huheran/MoveToPlay/hardware/pcb/Blade_V1.0_Nromal/Blade_V1.0_Nromal_.png

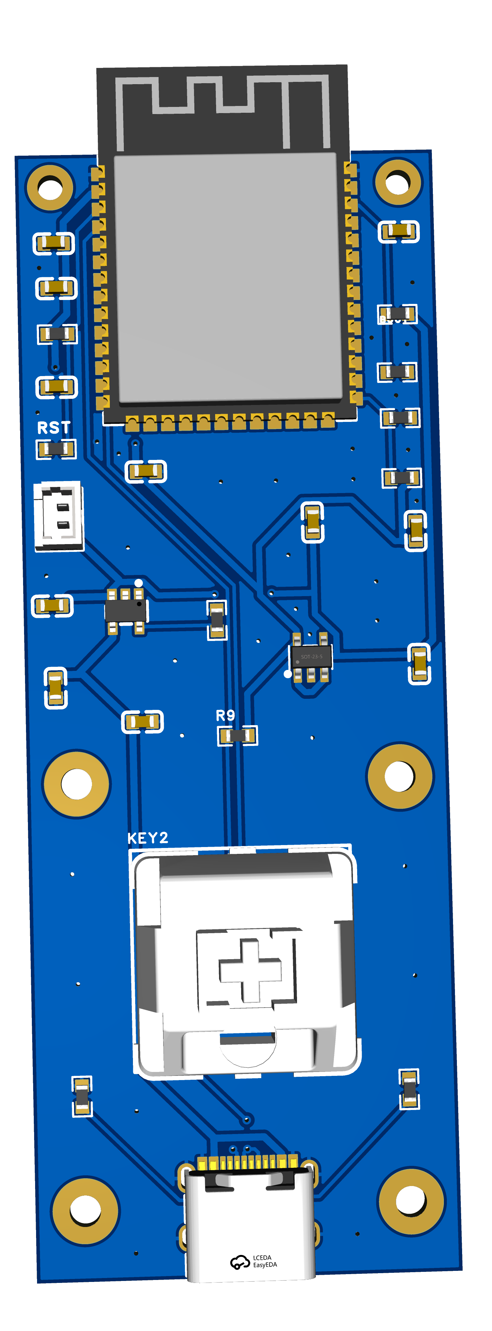
hardware/pcb/Blade_V1.0_Nromal/Blade_V1.0_Nromal_.png
