huheran/MoveToPlay/hardware/pcb/Blade_V2.0_HR(Heart Rate)/Blade_V2.0_HR(Heart Rate)-.png

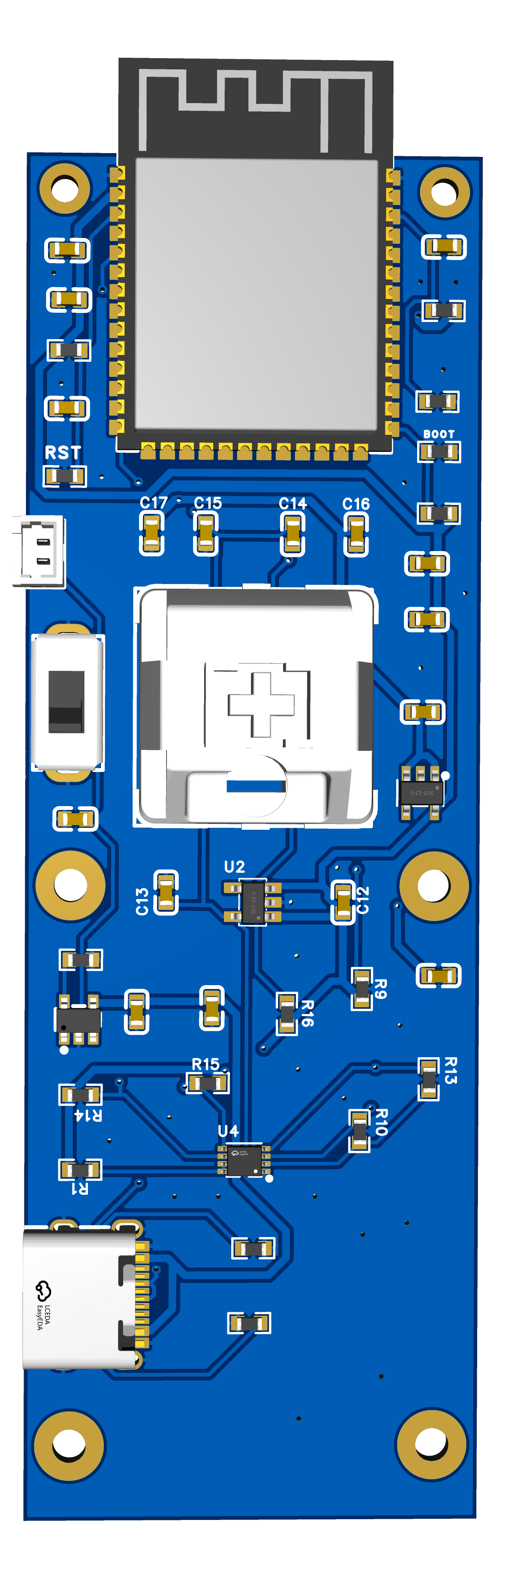
hardware/pcb/Blade_V2.0_HR(Heart Rate)/Blade_V2.0_HR(Heart Rate)-.png
