huheran/MoveToPlay/hardware/pcb/Dongle_SW1/Dongle_SW1.png

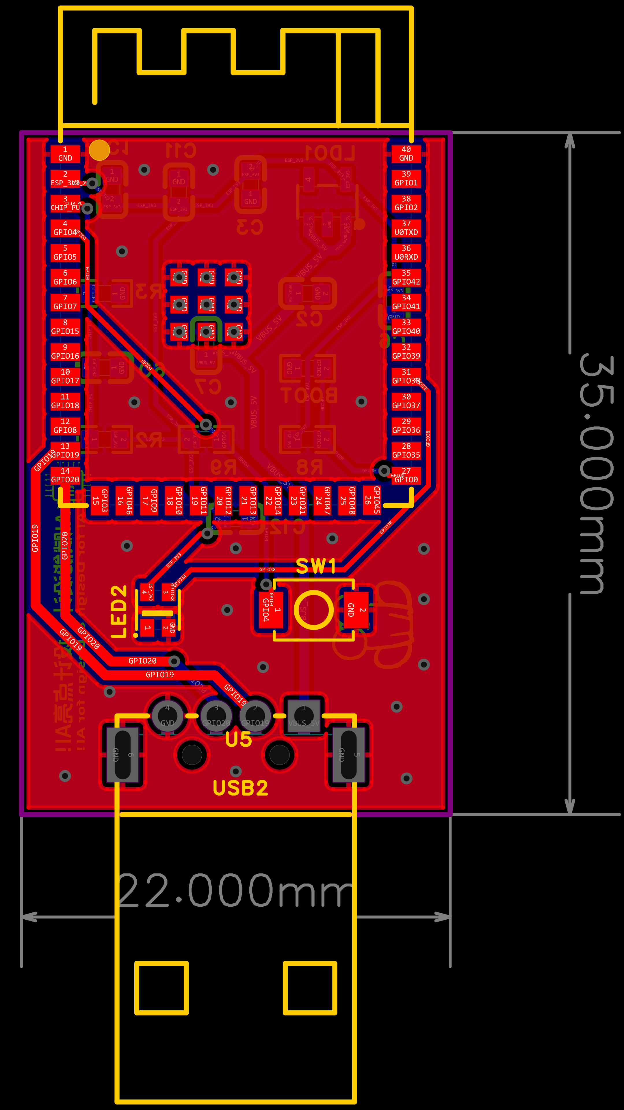
hardware/pcb/Dongle_SW1/Dongle_SW1.png
