huheran/MoveToPlay/hardware/pcb/Dongle_SW3/Dongle_SW3.png

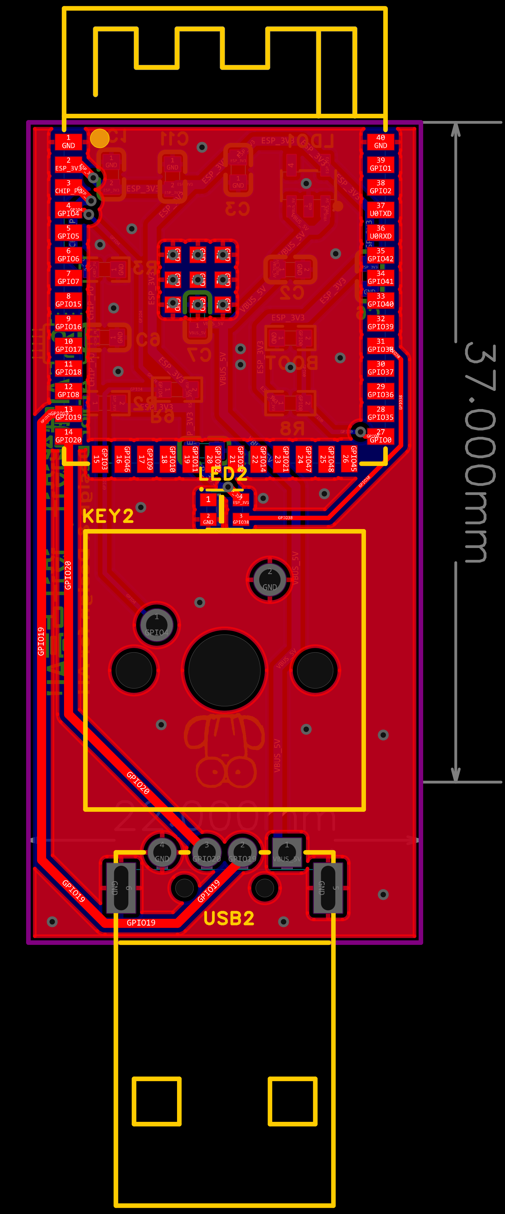
hardware/pcb/Dongle_SW3/Dongle_SW3.png
