huheran/MoveToPlay/hardware/pcb/Heart_Rate_V2.0/Heart_Rate_V2.0.png

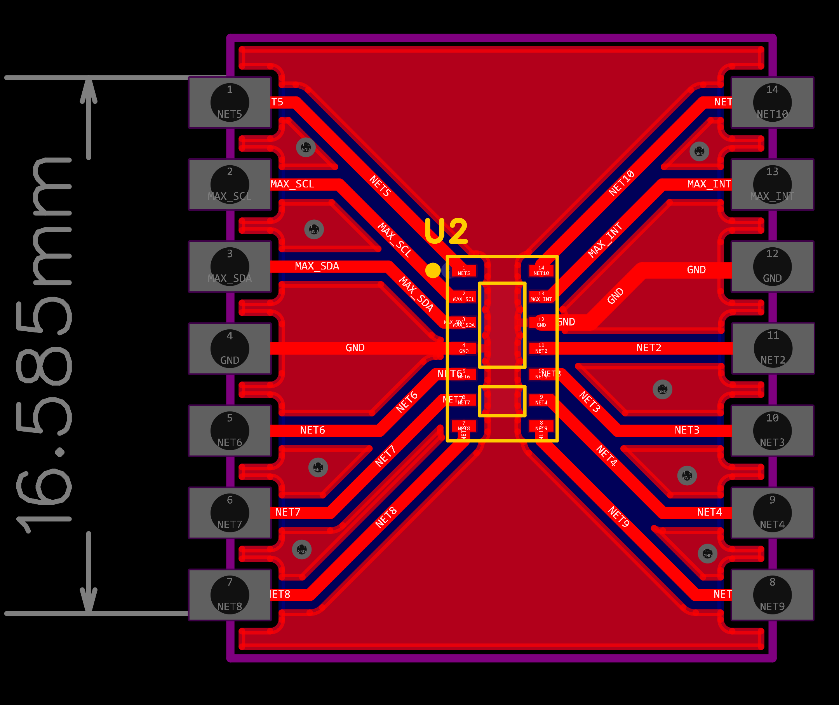
hardware/pcb/Heart_Rate_V2.0/Heart_Rate_V2.0.png
