huheran/MoveToPlay/hardware/pcb/Heart_Rate_V2.0/Heart_Rate_V2.0_.png

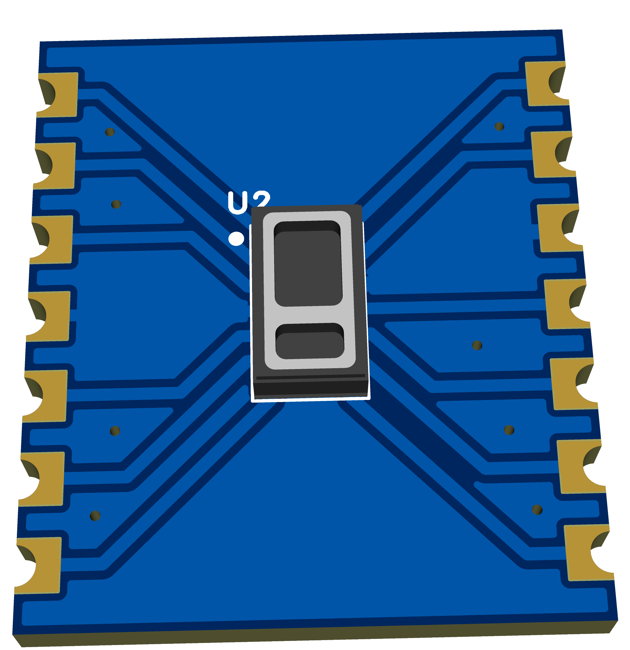
hardware/pcb/Heart_Rate_V2.0/Heart_Rate_V2.0_.png
