huheran/MoveToPlay/hardware/pcb/Tracker_V1.0_Top-Battery/Tracker_V1.0_Top-Battery_.png

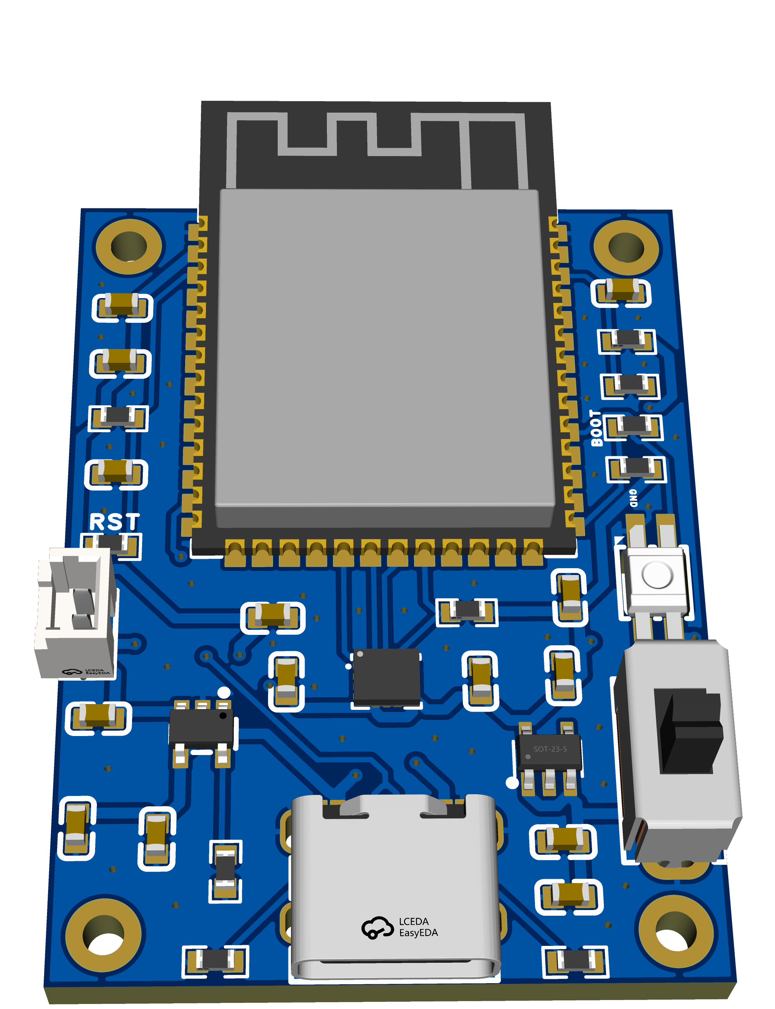
hardware/pcb/Tracker_V1.0_Top-Battery/Tracker_V1.0_Top-Battery_.png
