huheran/MoveToPlay/hardware/pcb/Tracker_V1.0_Top-Battery_SMT/Tracker_V1.0_SMT_Top-Battery-.png

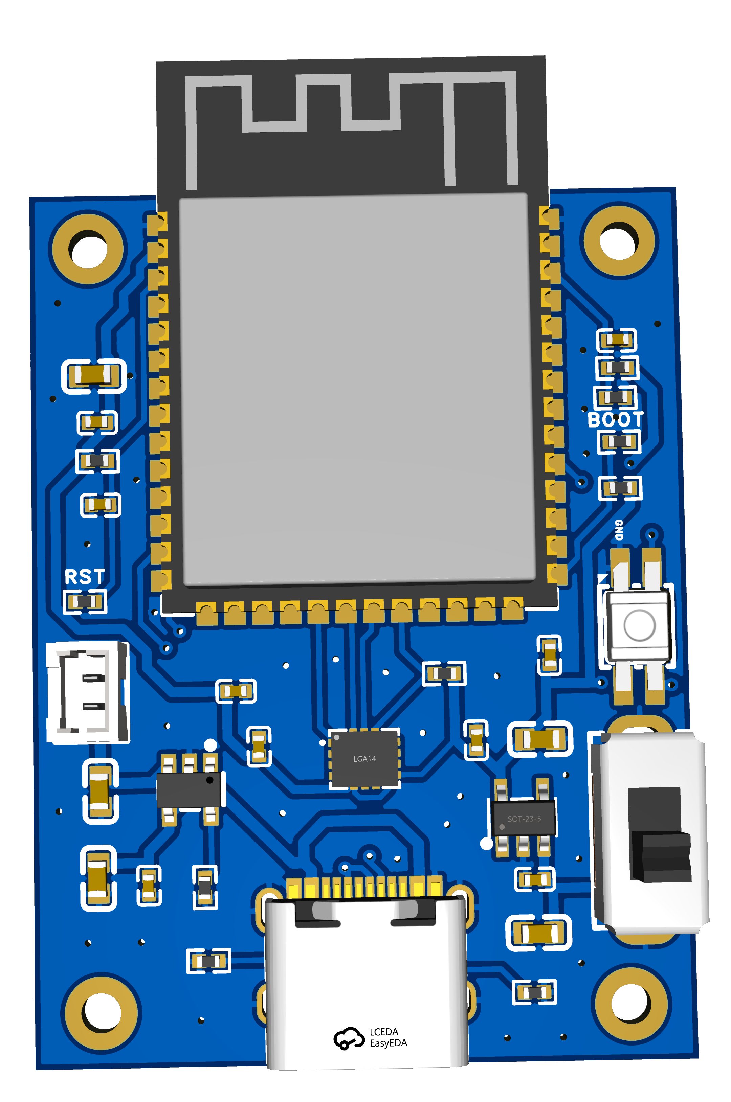
hardware/pcb/Tracker_V1.0_Top-Battery_SMT/Tracker_V1.0_SMT_Top-Battery-.png
