huheran/MoveToPlay/hardware/pcb/Tracker_V2.0_Botton-Battery/Tracker_V2.0_Botton-Battery.png

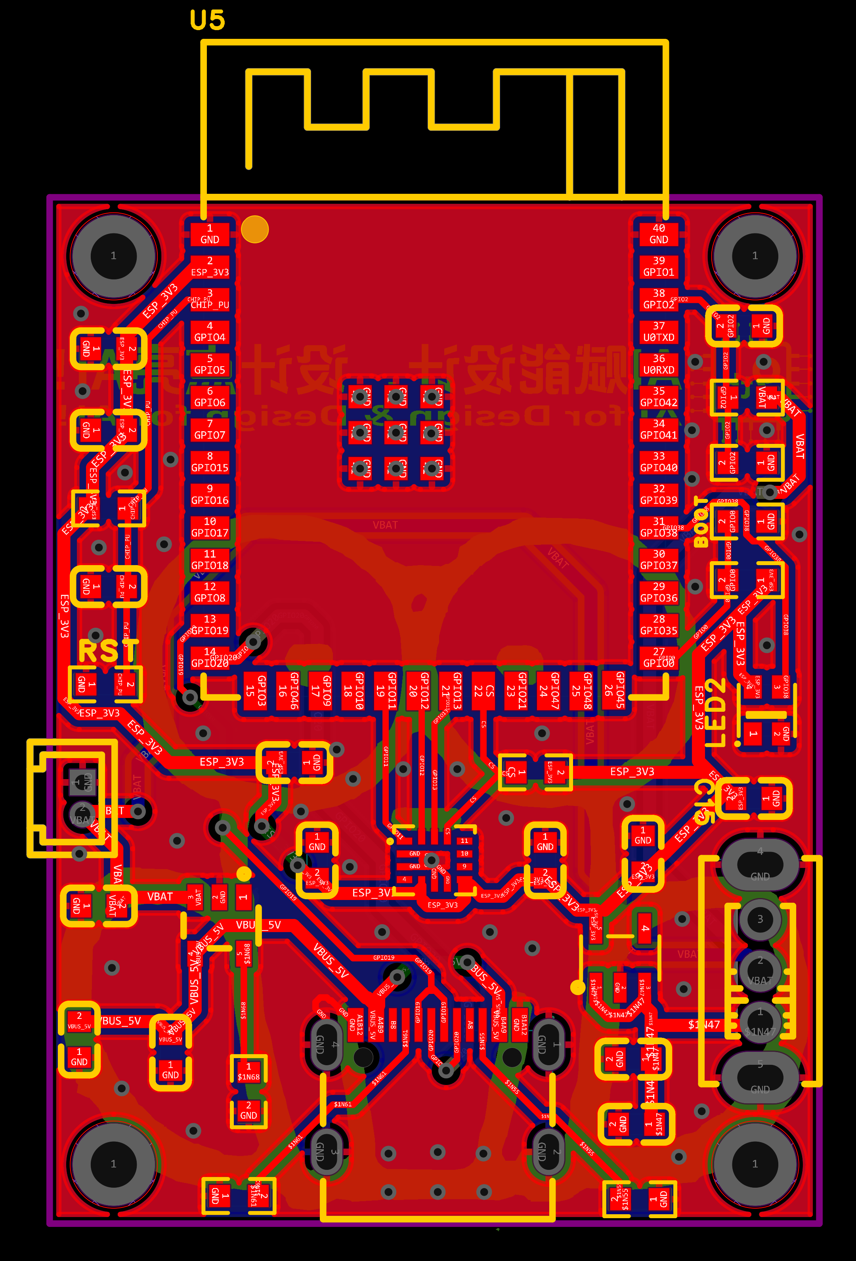
hardware/pcb/Tracker_V2.0_Botton-Battery/Tracker_V2.0_Botton-Battery.png
