huheran/MoveToPlay/hardware/pcb/Tracker_V2.0_Botton-Battery/Tracker_V2.0_Botton-Battery_.png

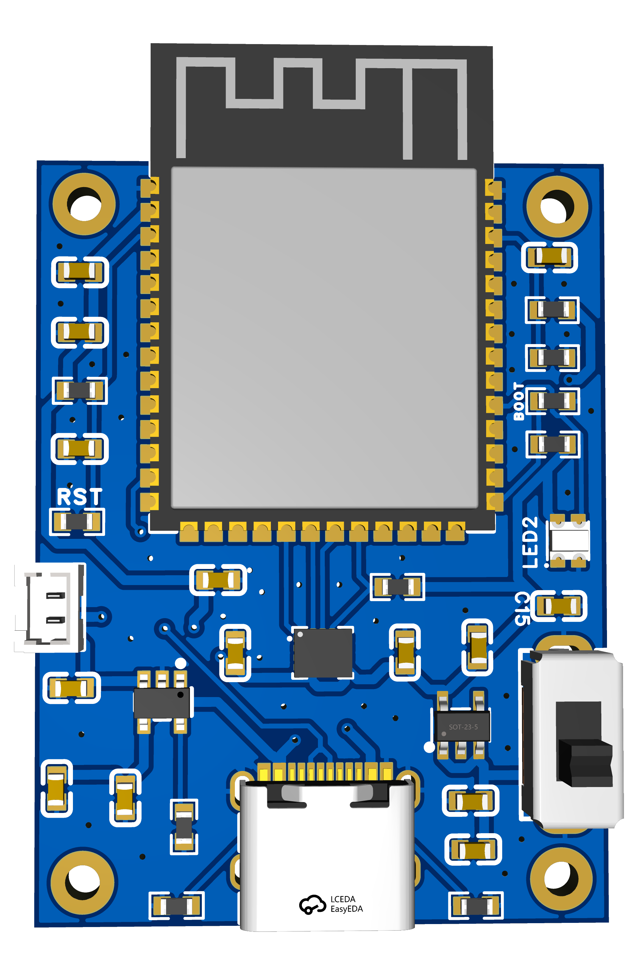
hardware/pcb/Tracker_V2.0_Botton-Battery/Tracker_V2.0_Botton-Battery_.png
