huheran/MoveToPlay/hardware/pcb/充电底座/充电底座.png

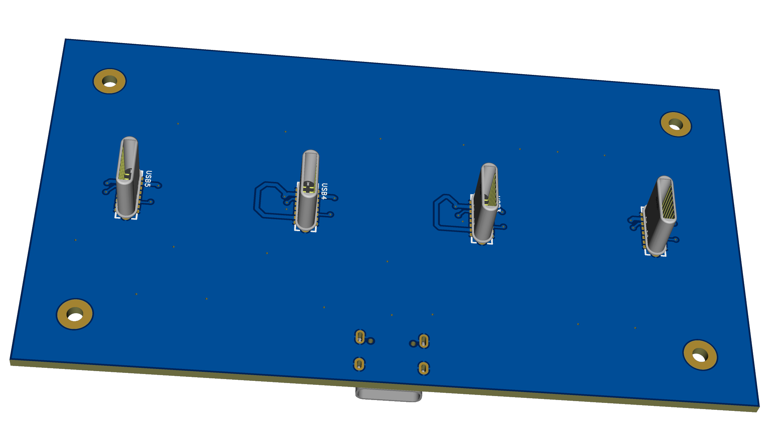
hardware/pcb/充电底座/充电底座.png
